3dpractical/SI_SCA/Hardware/ver1_0/Schema_pdf/ver1_0.pdf

A

A

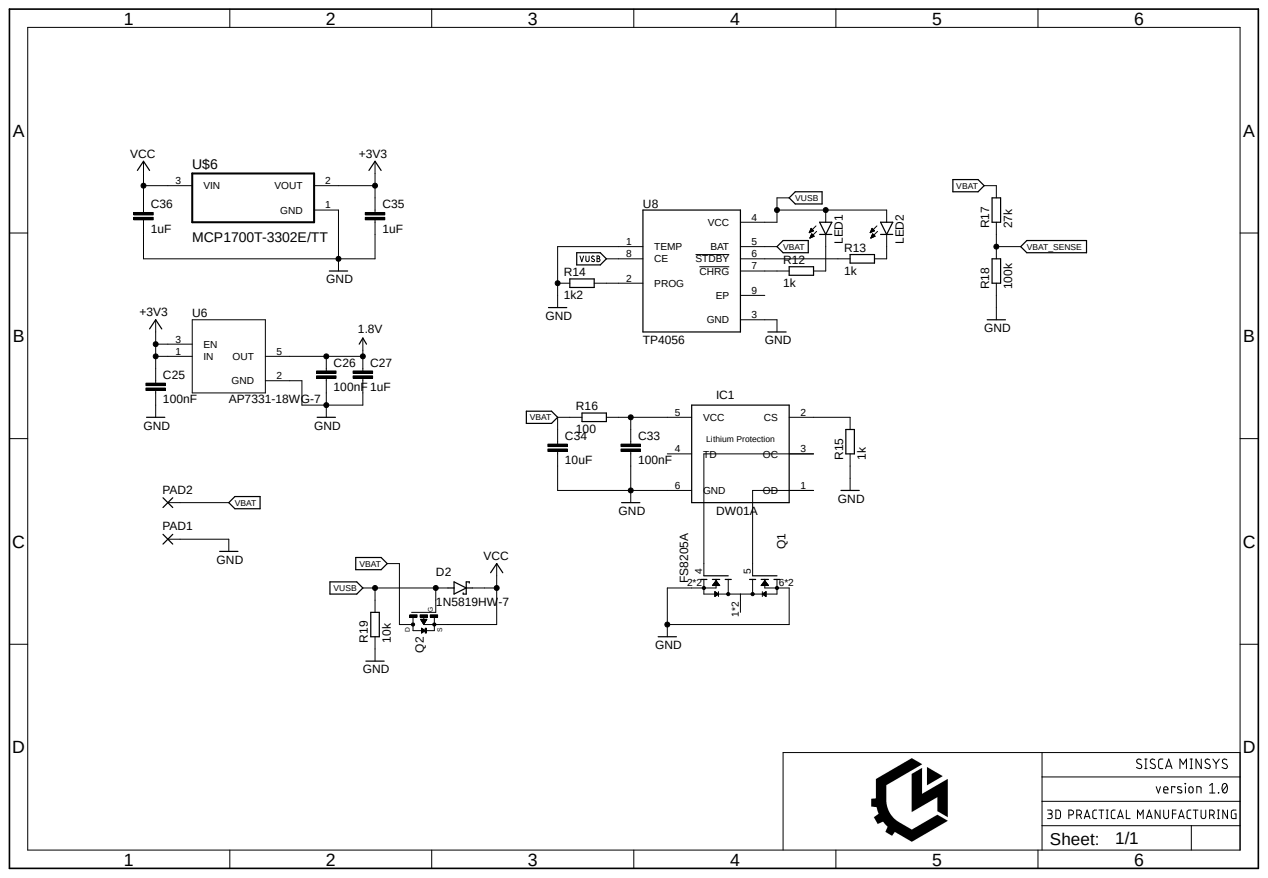
[picture p18: page 1]

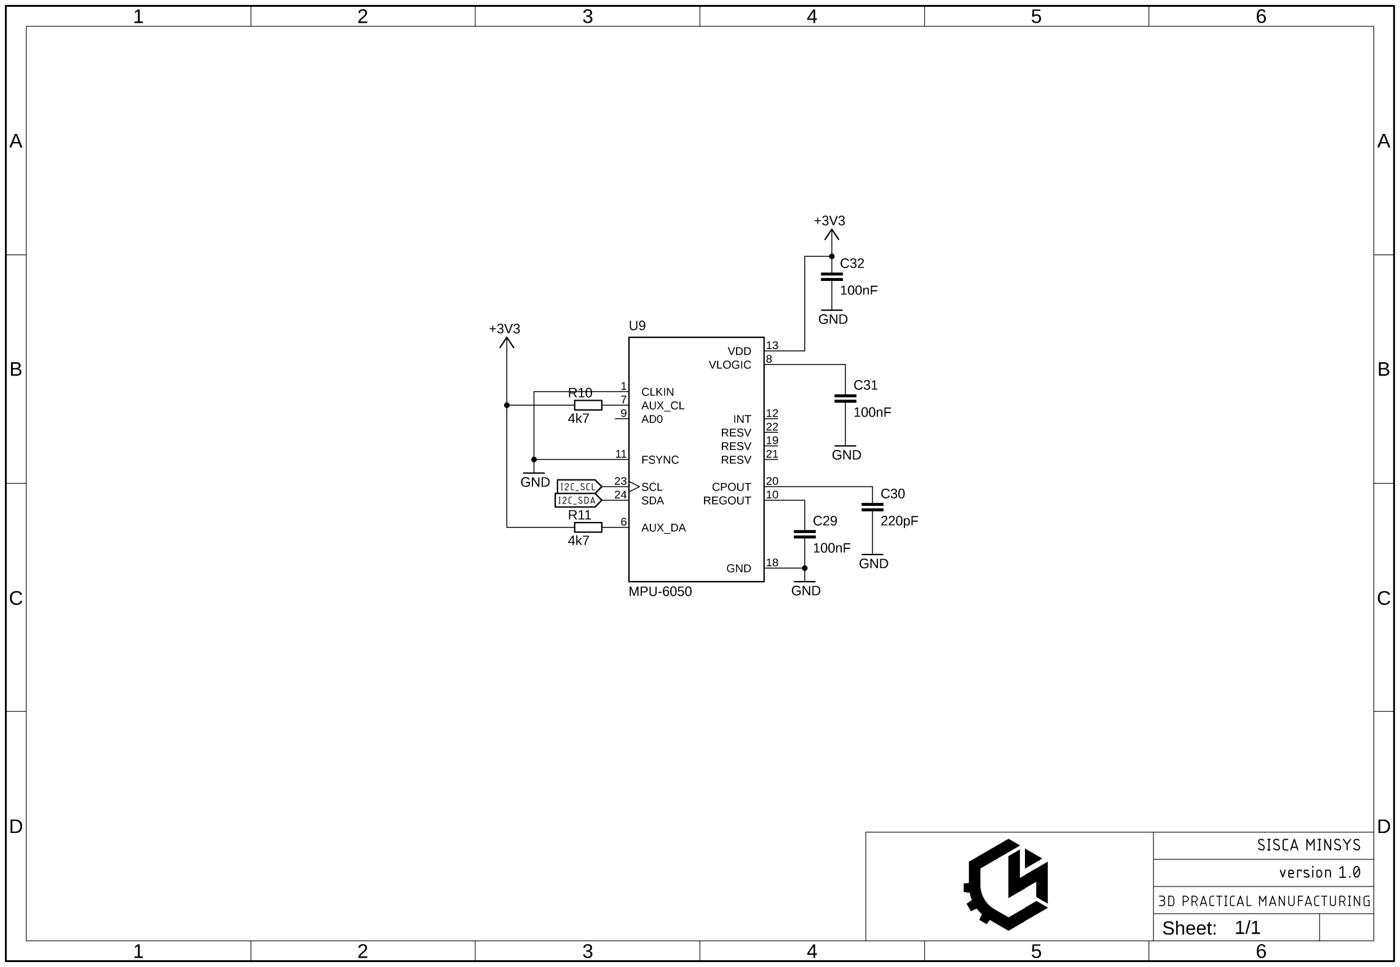
[picture p19: page 2]
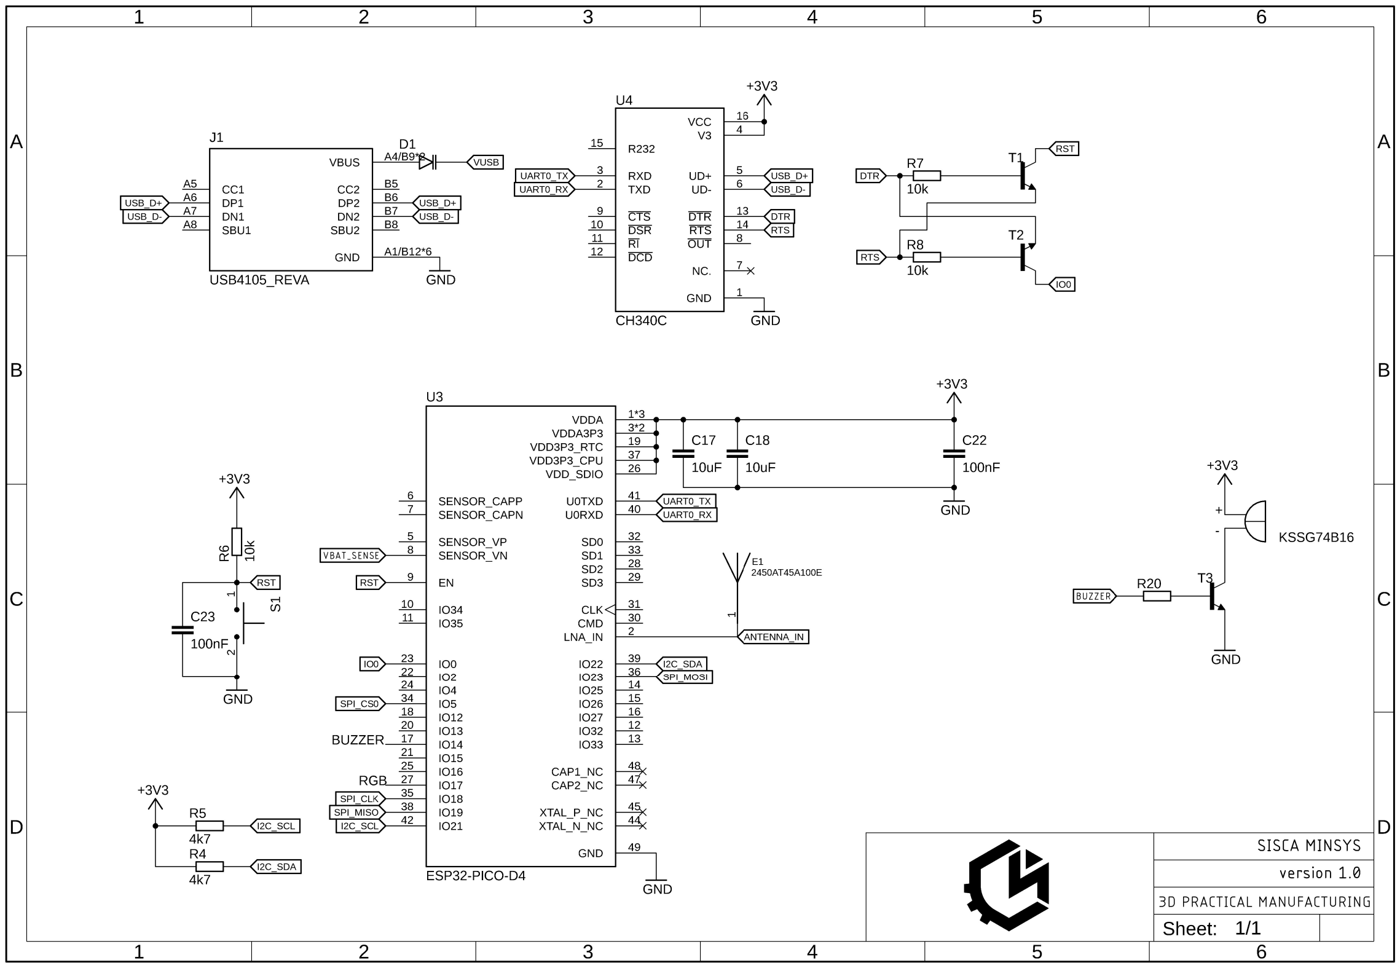
[picture p20: page 3]
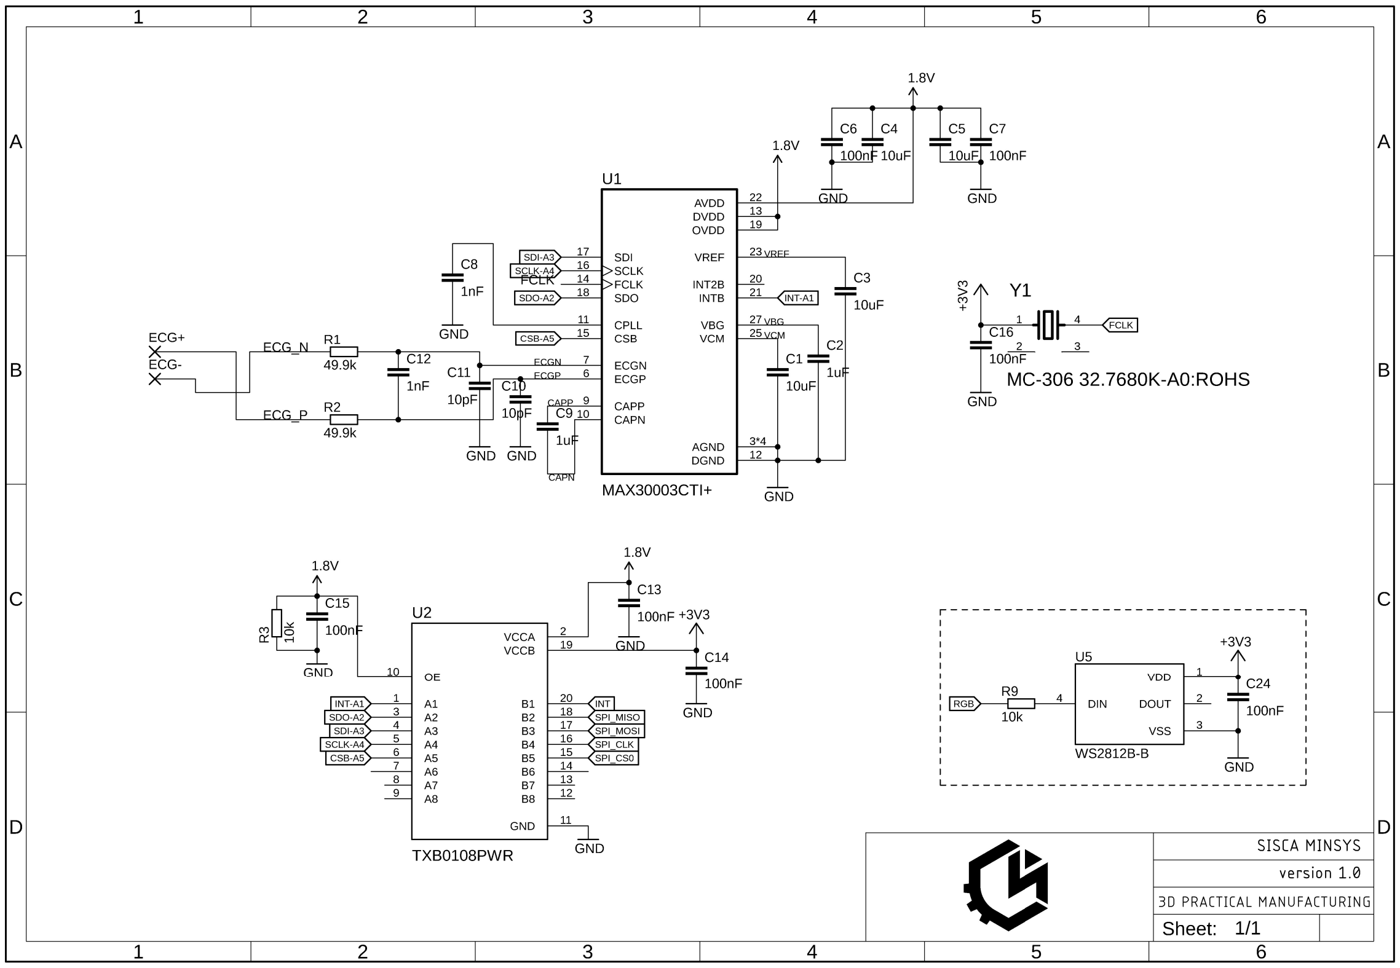
[picture p21: page 4]
