3dpractical/SI_SCA/Hardware/ver2_0/Schema_pdf/ver2_0.pdf

Sheet: ABCD | 1 | 2 | 3 | 4 | 5 | 6 | ABCD 1 | 2 | 3 | 4 | 5 | 6

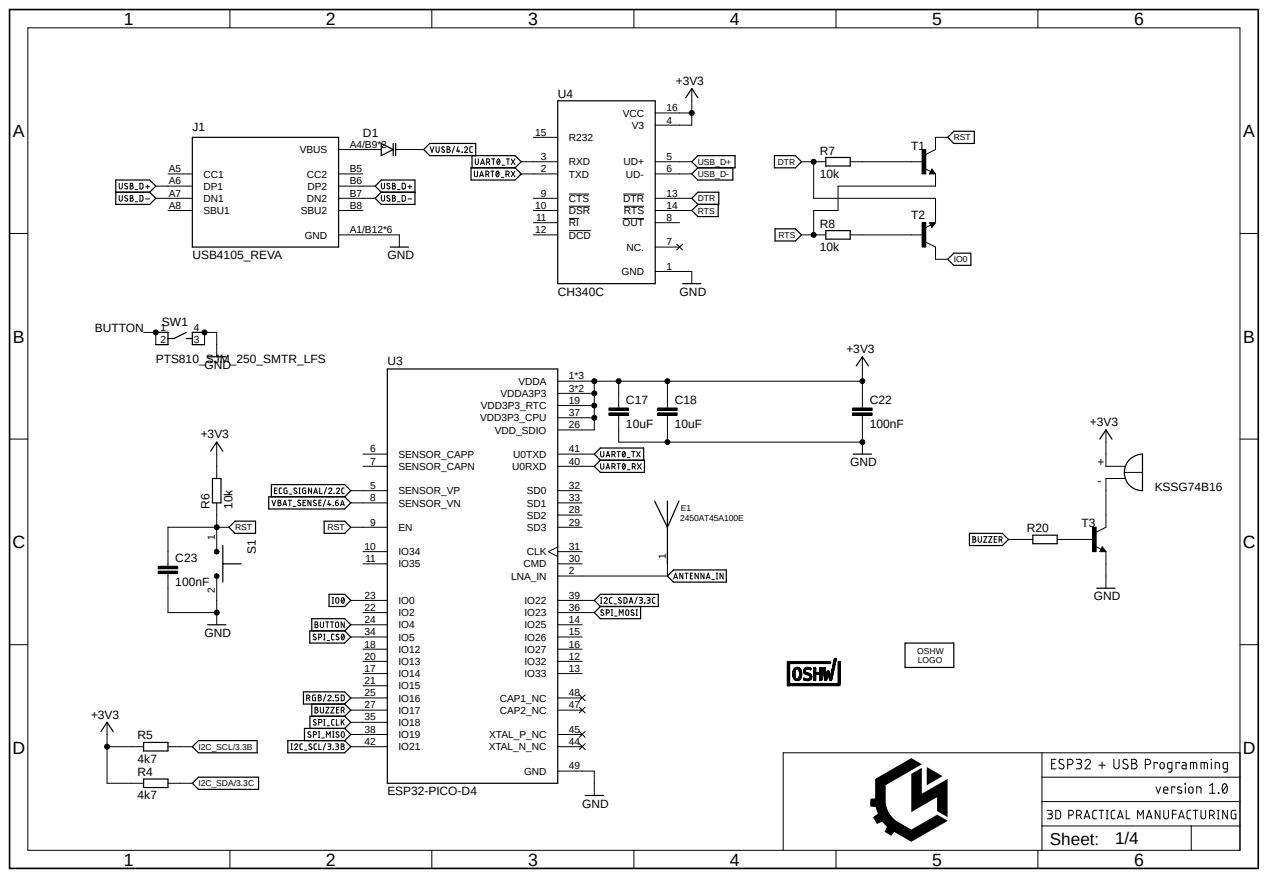
[picture p22: page 1]
