3dpractical/SI_SCA/Hardware/ver5_0/Render/image 1.png

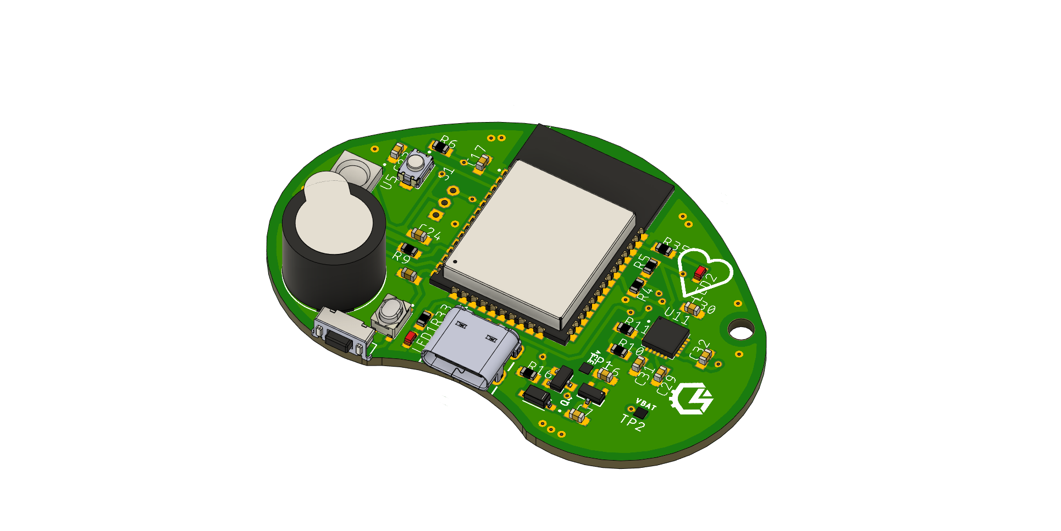
Hardware/ver5_0/Render/image 1.png
