3dpractical/SI_SCA/Hardware/ver5_0/Render/image 2.png

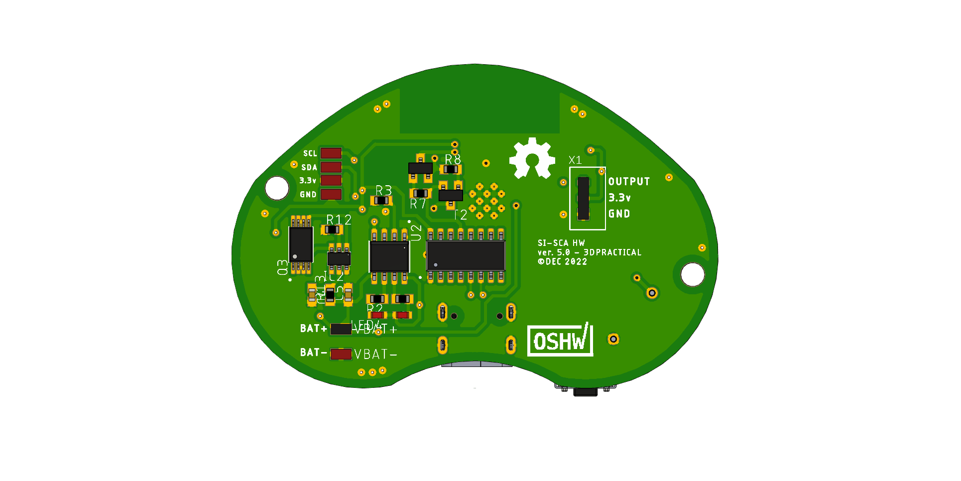
Hardware/ver5_0/Render/image 2.png
